alantrundle/StreamerBasic/src/A2DPCore.cpp

#include "A2DPCore.h"
#include <string.h>

#include "AudioCore.h"

// === AUTO-RECONNECT (NVS)
#include "nvs.h"
#include "nvs_flash.h"

#define AR_NAMESPACE "a2dp_ar"
#define AR_KEY       "table"
#define AR_MAX       10

typedef struct {
  uint8_t mac[6];
  char    name[32];
} AutoReconnectEntry;

// ------------------------------------------------------------
// Static storage
// ------------------------------------------------------------

A2DPCore* A2DPCore::self_ = nullptr;

esp_bd_addr_t A2DPCore::scan_bda_[MAX_SCAN];
char          A2DPCore::scan_name_[MAX_SCAN][32];
int8_t        A2DPCore::scan_rssi_[MAX_SCAN];
int           A2DPCore::scan_count_ = 0;

// === AUTO-RECONNECT (NVS)
static AutoReconnectEntry ar_table[AR_MAX];

static esp_timer_handle_t s_a2dp_kick_timer = nullptr;
static void a2dp_kick_cb(void* arg);


// ------------------------------------------------------------
// NVS helpers
// ------------------------------------------------------------

static void ar_init()
{
  nvs_handle_t nvs;
  if (nvs_open(AR_NAMESPACE, NVS_READWRITE, &nvs) != ESP_OK) return;

  size_t len = sizeof(ar_table);
  esp_err_t r = nvs_get_blob(nvs, AR_KEY, nullptr, &len);
  if (r == ESP_ERR_NVS_NOT_FOUND) {
    memset(ar_table, 0, sizeof(ar_table));
    nvs_set_blob(nvs, AR_KEY, ar_table, sizeof(ar_table));
    nvs_commit(nvs);
  }
  nvs_close(nvs);
}

static void ar_load()
{
  nvs_handle_t nvs;
  size_t len = sizeof(ar_table);
  if (nvs_open(AR_NAMESPACE, NVS_READONLY, &nvs) != ESP_OK) return;
  nvs_get_blob(nvs, AR_KEY, ar_table, &len);
  nvs_close(nvs);
}

static void ar_store()
{
  nvs_handle_t nvs;
  if (nvs_open(AR_NAMESPACE, NVS_READWRITE, &nvs) != ESP_OK) return;
  nvs_set_blob(nvs, AR_KEY, ar_table, sizeof(ar_table));
  nvs_commit(nvs);
  nvs_close(nvs);
}

void A2DPCore::erase_autoreconnect_table()
{
  memset(ar_table, 0, sizeof(ar_table));

  nvs_handle_t nvs;
  if (nvs_open(AR_NAMESPACE, NVS_READWRITE, &nvs) == ESP_OK) {

    nvs_erase_key(nvs, AR_KEY);
    nvs_commit(nvs);
    nvs_close(nvs);

    Serial.println("[A2DP] 🗑 Auto-reconnect table erased");
  } else {
    Serial.println("[A2DP] ❌ Failed to erase NV table");
  }
}


// ------------------------------------------------------------
// Ctor
// ------------------------------------------------------------

A2DPCore::A2DPCore() {
  self_ = this;
}

// ------------------------------------------------------------
// Configuration
// ------------------------------------------------------------

void A2DPCore::set_device_name(const char* name) {
  if (name) {
    strlcpy(device_name_, name, sizeof(device_name_));
  }
}

void A2DPCore::set_connectionstate_callback(A2DPConnectionStateCallback cb) {
  conn_cb_ = cb;
}

void A2DPCore::set_audiostate_callback(A2DPAudioStateCallback cb) {
  audio_cb_ = cb;
}

void A2DPCore::set_scan_callback(A2DPScanCallback cb) {
  scan_cb_ = cb;
}

void A2DPCore::set_pcm_callback(esp_a2d_source_data_cb_t cb) {
  pcm_cb_ = cb;
}

void A2DPCore::set_autoreconnection(bool enable) {
  auto_reconnect_ = enable;
  Serial.printf("[A2DP] 🔁 Auto-reconnect %s\n",
                enable ? "ENABLED" : "DISABLED");
}

// ------------------------------------------------------------
// Start Bluetooth stack
// ------------------------------------------------------------
void A2DPCore::start()
{
  ar_init();
  ar_load();

  if (!btStarted()) {
    if (!btStart()) {
      Serial.println("[BT] ❌ btStart failed");
      return;
    }
  }

  if (esp_bluedroid_get_status() == ESP_BLUEDROID_STATUS_UNINITIALIZED)
    esp_bluedroid_init();
  if (esp_bluedroid_get_status() != ESP_BLUEDROID_STATUS_ENABLED)
    esp_bluedroid_enable();

  esp_bt_gap_register_callback(gap_cb);
  esp_bt_gap_set_scan_mode(ESP_BT_CONNECTABLE,
                           ESP_BT_GENERAL_DISCOVERABLE);

  if (device_name_[0]) {
    esp_bt_dev_set_device_name(device_name_);
    Serial.printf("[BT] Device name: %s\n", device_name_);
  }

  esp_a2d_register_callback(a2dp_cb);
  if (pcm_cb_) esp_a2d_source_register_data_callback(pcm_cb_);
  esp_avrc_tg_register_callback(avrc_tg_cb);
  esp_avrc_tg_init();
  esp_a2d_source_init();

  // ===== AUTO-RECONNECT =====
  if (auto_reconnect_) {

    block_manual_scan_ = true;
    autoreconnect_start_ms_ = millis();

    for (int i = 0; i < AR_MAX; i++) {
      if (ar_table[i].mac[0] == 0x00)
        continue;

      Serial.printf("[A2DP] 🔁 Auto-connect: %s\n",
        ar_table[i].name[0] ? ar_table[i].name : "Unknown");

      connecting_via_autoreconnect_ = true;    // ✅ authoritative flag
      esp_a2d_source_connect(ar_table[i].mac);
      break;
    }
  }

  Serial.println("[A2DP] ✅ Source ready");
}

// ------------------------------------------------------------

void A2DPCore::loop() {
  if (!block_manual_scan_) return;

  if (millis() - autoreconnect_start_ms_ >= 5000) {
    block_manual_scan_ = false;
    Serial.println("[A2DP] 🔓 Manual scan unblocked");
  }
}

static bool ar_contains_mac(const uint8_t* mac)
{
    for (int i = 0; i < AR_MAX; i++) {
        if (ar_table[i].mac[0] &&
            memcmp(ar_table[i].mac, mac, 6) == 0) {
            return true;
        }
    }
    return false;
}

// ------------------------------------------------------------
// Scan / connect
// ------------------------------------------------------------

void A2DPCore::start_scan(uint32_t duration_seconds) {

  if (block_manual_scan_) {
    Serial.println("[A2DP] 🚫 Scan blocked");
    return;
  }

  scan_count_ = 0;
  scanning_   = true;

  Serial.printf("[BT] 🔍 Scanning (%u sec)\n", duration_seconds);

  esp_bt_gap_start_discovery(ESP_BT_INQ_MODE_GENERAL_INQUIRY,
                             duration_seconds, 0);
}

void A2DPCore::stop_scan() {
  esp_bt_gap_cancel_discovery();
}

void A2DPCore::connect_by_index(int index)
{
  if (index < 0 || index >= scan_count_)
    return;

  // Manual connection overrides auto-reconnect
  connecting_via_autoreconnect_ = false;

  for (int i = 0; i < AR_MAX; i++) {
    if (ar_table[i].mac[0] == 0x00) {
      memcpy(ar_table[i].mac, scan_bda_[index], 6);
      strncpy(ar_table[i].name,
              scan_name_[index][0]
                ? scan_name_[index]
                : "Unknown",
              sizeof(ar_table[i].name) - 1);
      ar_store();

      Serial.printf("[A2DP] 💾 Stored NV[%d]: %s\n",
                    i, ar_table[i].name);
      break;
    }
  }

  esp_a2d_source_connect(scan_bda_[index]);
}

// ------------------------------------------------------------
// Delete NV entry
// ------------------------------------------------------------

void A2DPCore::autoreconnect_delete(int index) {
  if (index < 0 || index >= AR_MAX) return;
  memset(&ar_table[index], 0, sizeof(AutoReconnectEntry));
  ar_store();
  Serial.printf("[A2DP] 🗑 Deleted NV[%d]\n", index);
}

bool A2DPCore::connected_details(A2DPConnectedDetails& out)
{
  if (!connected_details_.connected)
    return false;

  out = connected_details_;
  return true;
}

// ------------------------------------------------------------
// GAP callback (EIR name support)
// ------------------------------------------------------------

void A2DPCore::gap_cb(esp_bt_gap_cb_event_t event,
                      esp_bt_gap_cb_param_t* param)
{
  if (!self_) return;

  switch (event) {

    // --------------------------------------------------
    // DEVICE FOUND
    // --------------------------------------------------
    case ESP_BT_GAP_DISC_RES_EVT: {

      if (scan_count_ >= MAX_SCAN) break;

      memcpy(scan_bda_[scan_count_],
             param->disc_res.bda,
             sizeof(esp_bd_addr_t));

      scan_name_[scan_count_][0] = '\0';
      scan_rssi_[scan_count_] = -127;

      uint8_t* eir = nullptr;

      // ------------------------------
      // Collect EIR + RSSI
      // ------------------------------
      for (int i = 0; i < param->disc_res.num_prop; i++) {

        esp_bt_gap_dev_prop_t* p = &param->disc_res.prop[i];

        if (p->type == ESP_BT_GAP_DEV_PROP_EIR && p->val) {
          eir = (uint8_t*)p->val;
        }
        else if (p->type == ESP_BT_GAP_DEV_PROP_RSSI && p->val) {
          scan_rssi_[scan_count_] = *(int8_t*)p->val;
        }
      }

      // ------------------------------
      // Resolve name from EIR
      // ------------------------------
      if (eir) {

        uint8_t name_len = 0;
        uint8_t* name = esp_bt_gap_resolve_eir_data(
            eir,
            ESP_BT_EIR_TYPE_CMPL_LOCAL_NAME,
            &name_len);

        if (!name) {
          name = esp_bt_gap_resolve_eir_data(
              eir,
              ESP_BT_EIR_TYPE_SHORT_LOCAL_NAME,
              &name_len);
        }

        if (name && name_len > 0) {

          size_t copy_len = name_len;
          if (copy_len >= sizeof(scan_name_[scan_count_]))
            copy_len = sizeof(scan_name_[scan_count_]) - 1;

          memcpy(scan_name_[scan_count_], name, copy_len);
          scan_name_[scan_count_][copy_len] = '\0';

          // ✅ HARD TRIM TRAILING NON-ASCII JUNK
          for (int i = copy_len - 1; i >= 0; i--) {
            uint8_t c = scan_name_[scan_count_][i];
            if (c >= 32 && c <= 126) break;
            scan_name_[scan_count_][i] = '\0';
          }
        }
      }

      Serial.printf(
        "[BT] 📡 Found: %s RSSI=%d\n",
        scan_name_[scan_count_][0]
          ? scan_name_[scan_count_]
          : "Unknown",
        scan_rssi_[scan_count_]
      );

      scan_count_++;
      break;
    }

    // --------------------------------------------------
    // SCAN STATE CHANGED
    // --------------------------------------------------
    case ESP_BT_GAP_DISC_STATE_CHANGED_EVT: {

      if (param->disc_st_chg.state ==
          ESP_BT_GAP_DISCOVERY_STOPPED) {

        self_->scanning_ = false;

        Serial.printf(
          "[BT] ✅ Scan complete (%d device%s)\n",
          scan_count_,
          scan_count_ == 1 ? "" : "s"
        );

        if (self_->scan_cb_) {

          static const char* names[MAX_SCAN];
          static const char* macs[MAX_SCAN];
          static char macbuf[MAX_SCAN][18];

          for (int i = 0; i < scan_count_; i++) {

            names[i] = scan_name_[i][0]
                       ? scan_name_[i]
                       : "Unknown";

            snprintf(macbuf[i], sizeof(macbuf[i]),
                     "%02X:%02X:%02X:%02X:%02X:%02X",
                     scan_bda_[i][0], scan_bda_[i][1],
                     scan_bda_[i][2], scan_bda_[i][3],
                     scan_bda_[i][4], scan_bda_[i][5]);

            macs[i] = macbuf[i];
          }

          self_->scan_cb_(scan_count_, names, macs, scan_rssi_);
        }
      }
      break;
    }

    default:
      break;
  }
}

// ------------------------------------------------------------
// A2DP callback (UNCHANGED)
// ------------------------------------------------------------

static esp_timer_handle_t s_kick = nullptr;

static void kick_cb(void*) {
  esp_a2d_media_ctrl(ESP_A2D_MEDIA_CTRL_CHECK_SRC_RDY);
}

static void a2dp_kick_cb(void* arg)
{
  esp_err_t r = esp_a2d_media_ctrl(ESP_A2D_MEDIA_CTRL_CHECK_SRC_RDY);
  if (r != ESP_OK) {
    Serial.printf("[A2DP] ❌ CHECK_SRC_RDY failed: %s\n",
                  esp_err_to_name(r));
  } else {
    Serial.println("[A2DP] ✅ CHECK_SRC_RDY sent (deferred)");
  }
}

void A2DPCore::a2dp_cb(esp_a2d_cb_event_t event,
                       esp_a2d_cb_param_t* param)
{
  if (!self_)
    return;

  switch (event) {

  // ==========================================================
  // CONNECTION STATE
  // ==========================================================
  case ESP_A2D_CONNECTION_STATE_EVT: {

    esp_a2d_connection_state_t s = param->conn_stat.state;
    Serial.printf("[A2DP] 🔗 Connection state = %d\n", s);

    // ===================== CONNECTED =====================
    if (s == ESP_A2D_CONNECTION_STATE_CONNECTED) {

      esp_bt_sleep_disable();

      self_->connected_ = true;
      self_->block_manual_scan_ = false;

      // Audio not ready until START ACK
      AudioCore::set_a2dp_audio_ready(false);

      // Clear + populate connected details
      memset(&self_->connected_details_, 0,
             sizeof(self_->connected_details_));

      self_->connected_details_.connected = true;

      // ✅ AUTHORITATIVE: connection source
      self_->connected_details_.auto_reconnect =
          ar_contains_mac(param->conn_stat.remote_bda);

      // One-shot flag — clear immediately
      self_->connecting_via_autoreconnect_ = false;

      // Store MAC
      memcpy(self_->connected_details_.mac,
             param->conn_stat.remote_bda, 6);

      // -------- Resolve name (priority order) --------
      // 1) Auto-reconnect table
      for (int i = 0; i < AR_MAX; i++) {
        if (ar_table[i].mac[0] &&
            memcmp(ar_table[i].mac,
                   param->conn_stat.remote_bda, 6) == 0) {

          strncpy(self_->connected_details_.name,
                  ar_table[i].name,
                  sizeof(self_->connected_details_.name) - 1);
          break;
        }
      }

      // 2) Last scan results
      if (!self_->connected_details_.name[0]) {
        for (int i = 0; i < scan_count_; i++) {
          if (memcmp(scan_bda_[i],
                     param->conn_stat.remote_bda, 6) == 0) {

            strncpy(self_->connected_details_.name,
                    scan_name_[i][0]
                      ? scan_name_[i]
                      : "Unknown",
                    sizeof(self_->connected_details_.name) - 1);
            break;
          }
        }
      }

      // 3) Fallback
      if (!self_->connected_details_.name[0]) {
        strncpy(self_->connected_details_.name,
                "Unknown",
                sizeof(self_->connected_details_.name) - 1);
      }

      Serial.printf(
        "[A2DP] ✅ Connected: %s (%02X:%02X:%02X:%02X:%02X:%02X) [%s]\n",
        self_->connected_details_.name,
        self_->connected_details_.mac[0],
        self_->connected_details_.mac[1],
        self_->connected_details_.mac[2],
        self_->connected_details_.mac[3],
        self_->connected_details_.mac[4],
        self_->connected_details_.mac[5],
        self_->connected_details_.auto_reconnect ? "AUTO" : "MANUAL"
      );

      // ---- Defer CHECK_SRC_RDY (required) ----
      if (!s_a2dp_kick_timer) {
        esp_timer_create_args_t args = {};
        args.callback = &a2dp_kick_cb;
        args.name     = "a2dp_kick";
        esp_timer_create(&args, &s_a2dp_kick_timer);
      }

      esp_timer_start_once(s_a2dp_kick_timer, 100000); // 100 ms
    }

    // ===================== DISCONNECTED =====================
    else if (s == ESP_A2D_CONNECTION_STATE_DISCONNECTED) {

      esp_bt_sleep_enable();

      self_->connected_ = false;
      self_->connecting_via_autoreconnect_ = false;

      AudioCore::set_a2dp_audio_ready(false);

      memset(&self_->connected_details_, 0,
             sizeof(self_->connected_details_));

      Serial.println("[A2DP] ❌ Device disconnected");
    }

    // Notify application
    if (self_->conn_cb_) {
      self_->conn_cb_(s, nullptr);
    }
    break;
  }

  // ==========================================================
  // MEDIA CONTROL ACKS (AUTHORITATIVE STREAM CONTROL)
  // ==========================================================
  case ESP_A2D_MEDIA_CTRL_ACK_EVT: {

    auto cmd = param->media_ctrl_stat.cmd;
    auto st  = param->media_ctrl_stat.status;

    if (cmd == ESP_A2D_MEDIA_CTRL_CHECK_SRC_RDY &&
        st  == ESP_A2D_MEDIA_CTRL_ACK_SUCCESS) {

      Serial.println("[A2DP] ▶ Source ready — starting stream");

      esp_err_t r =
        esp_a2d_media_ctrl(ESP_A2D_MEDIA_CTRL_START);

      if (r != ESP_OK) {
        Serial.printf("[A2DP] ❌ START failed: %s\n",
                      esp_err_to_name(r));
      }
    }

    if (cmd == ESP_A2D_MEDIA_CTRL_START &&
        st  == ESP_A2D_MEDIA_CTRL_ACK_SUCCESS) {

      Serial.println("[A2DP] ✅ Media START confirmed");
      AudioCore::set_a2dp_audio_ready(true);
    }

    if (cmd == ESP_A2D_MEDIA_CTRL_STOP ||
        cmd == ESP_A2D_MEDIA_CTRL_SUSPEND) {

      Serial.println("[A2DP] ⏹ Media stopped");
      AudioCore::set_a2dp_audio_ready(false);
    }

    break;
  }

  // ==========================================================
  // AUDIO STATE (informational only)
  // ==========================================================
  case ESP_A2D_AUDIO_STATE_EVT: {

    if (self_->audio_cb_) {
      self_->audio_cb_(param->audio_stat.state, nullptr);
    }
    break;
  }

  default:
    break;
  }
}


// ------------------------------------------------------------

void A2DPCore::avrc_tg_cb(esp_avrc_tg_cb_event_t,
                          esp_avrc_tg_cb_param_t*) {}
